Eidon-AI/eidon-tracker/whitepaper-styled.html

# EIDON TRACKER SYSTEM

## A High-Precision Wearable IMU Platform for Embodied AI Training Data Collection

Eidon Tracker - Technical illustration

Eidon Tracker - Technical illustration

Version 1.0 Date: November 2025

## Table of Contents

1. Executive Summary
2. System Overview
3. Hardware Platform
4. Firmware & Embedded Software
5. Data Collection & Processing Pipeline
6. Mathematical Framework
7. Integration Ecosystem
8. Applications & Use Cases
9. Technical Specifications
10. Conclusion

## 1. Executive Summary

### The Embodied AI Data Challenge

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

### The Eidon Solution

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

Key Value Propositions:

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

### The “LLM Moment” for Humanoid Robotics

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

## 2. System Overview

### Architecture

The Eidon ecosystem consists of three integrated subsystems:

System Architecture Diagram - Complete ecosystem from capture to training

System Architecture Diagram - Complete ecosystem from capture to training

#### 2.1 Eidon Tracker Hardware

Seven wearable IMU devices providing real-time orientation tracking:

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

#### 2.2 Mobile Application Hub

Smartphone app serving as central data aggregator:

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

#### 2.3 Data Processing Pipeline (eidon-sim)

Real-time and post-processing kinematics engine:

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

### Data Flow

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

┌─────────────────────────────────────────────────────────────────────┐
│  TRAINING PHASE (VLA Pipeline)                                      │
├─────────────────────────────────────────────────────────────────────┤
│  Processed Dataset ──► VLA Training ──► Humanoid Control Policy    │
└─────────────────────────────────────────────────────────────────────┘

### Wearing Configuration

Body Tracking Layout - Front and side view showing 7 tracker placement positions

Body Tracking Layout - Front and side view showing 7 tracker placement positions

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

Tracker Mounting Details - Close-up showing strap mounting and attachment mechanism

Tracker Mounting Details - Close-up showing strap mounting and attachment mechanism

### Key System Specifications (Summary)

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

## 3. Hardware Platform

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

### 3.1 Custom PCB Design

PCB Design - Custom circuit board layout and schematic

PCB Design - Custom circuit board layout and schematic

#### PCB Specifications

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

#### Key Components

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

#### Power Subsystem

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

#### Communication Interfaces

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

### 3.2 Mechanical Design

Exploded View Assembly - CAD rendering showing all components separated

Exploded View Assembly - CAD rendering showing all components separated

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

Exploded View Assembly - Side perspective showing internal layout

Exploded View Assembly - Side perspective showing internal layout

#### Enclosure Specifications

Current Design: Version 3b (eidon-tracker-v3b)

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

#### Mounting System

Arm Mount - Elastic strap mounting on forearm Chest Mount - Harness system for torso tracking

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

#### Manufacturing Considerations

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

### 3.3 Bill of Materials (Complete Device)

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

Complete 7-Device Kit (Ready to Use):

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

## 4. Firmware & Embedded Software

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

Firmware Architecture Diagram - Layered software architecture and data flow

### 4.1 Development Environment

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

### 4.2 Core Firmware Capabilities

#### A. IMU Sensor Integration

Sensor configuration (from firmware/lib/BNO085/BNO085.cpp):

// Initialize I2C communication at 400kHz
Wire.setPins(SDA_PIN, SCL_PIN);  // GPIO20, GPIO19
Wire.begin();
Wire.setClock(400000);

// Configure BNO085 for game rotation vector mode
bno08x.enableReport(SH2_GAME_ROTATION_VECTOR, 20833);  // 48Hz (20.83ms)

Data acquisition loop (48Hz):

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

#### B. Dual-Radio Wireless Architecture

The firmware implements a unique BLE + ESP-NOW dual-protocol system for efficient multi-device coordination.

BLE (Bluetooth Low Energy) - Primary Interface:

Custom GATT service: E1D00001-8B5A-3E5B-9E23-4F9B5C91BBDE

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

BLE notification rate: 24Hz (42ms intervals) to balance throughput and power

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

ESP-NOW - Child-to-Hub Communication:

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

Protocol details:

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

#### C. Device Role System

Seven role types (configured via BLE characteristic E1D00007):

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

#### D. Power Management

Battery monitoring (firmware/src/main.cpp):

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

Update interval: Every 5 seconds (balances accuracy and ADC power consumption)

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

#### E. LED Status Indicators

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

Auxiliary LED (GPIO1) - Secondary indicator: - Blinking: Advertising - Solid: Connected

### 4.3 Firmware Performance Metrics

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

### 4.4 Firmware File Structure

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

## 5. Data Collection & Processing Pipeline

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

### 5.1 Mobile Application Hub

Platform: iOS/Android (Flutter framework)

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

Mobile App Screenshot - Data collection interface with device status and recording controls

Mobile App Screenshot - Data collection interface with device status and recording controls

### 5.2 Quaternion Data Format

Raw quaternion packet (from BLE characteristic):

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

Device info packet (characteristic E1D00005):

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

### 5.3 eidon-sim Processing Engine

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

#### Core Processing Modules

A. Quaternion Decoder (src/core/reportParsers.ts)

Converts raw binary quaternion data to usable format:

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

Coordinate frame transformation (sensor → Three.js world):

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

B. Seven-Degree-of-Freedom Arm Solver (src/core/ArmSolver.ts)

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

Elbow joint (1-DOF): 4. Flex (flexion/extension angle)

Forearm (1-DOF): 5. Roll (pronation/supination)

Wrist joint (2-DOF): 6. Yaw (ulnar/radial deviation) 7. Pitch (flexion/extension)

Algorithmic approach (detailed in Section 6: Mathematical Framework)

C. 3D Skeletal Visualization (src/ui/scene/)

Two rendering modes:

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

D. Temporal Filtering

To reduce high-frequency noise from IMU drift and vibration:

Angle unwrapping (prevents discontinuities at ±180°):

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

Exponential moving average (EMA smoothing):

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

### 5.4 Output Data Products

The eidon-sim pipeline generates multiple output formats:

1. Joint Angle Time Series (CSV)

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

2. 3D Skeletal Positions (JSON)

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

3. Video with Overlay (MP4)

Synchronized video with: - On-screen joint angle readouts - Skeleton overlay (optional) - Timestamp and session metadata

4. VLA Training Format

Proposed structure (compatible with common VLA frameworks):

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

Action labeling: - Manual annotation via UI timeline - Future: GPT-4V automatic segmentation from video

## 6. Mathematical Framework

This section details the mathematical transformations that convert raw IMU quaternions into anatomically meaningful joint angles.

Quaternion to Angles Overview - Mathematical transformation pipeline

### 6.1 Quaternion Fundamentals

Definition:

A quaternion q is a 4-dimensional number representing 3D rotation:

q = w + xi + yj + zk

where i² = j² = k² = ijk = -1

Vector form: q = [x, y, z, w] (or [qx, qy, qz, qw])

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

Quaternion multiplication (Hamilton product):

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

Rotating a vector v by quaternion q:

v' = q ⊗ [0, v] ⊗ q⁻¹

Implemented efficiently as:

vec3.transformQuat(out, v, q)

### 6.2 Quaternion to Rotation Matrix

The quaternion q = [x, y, z, w] converts to a 3×3 rotation matrix:

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

Code implementation (src/core/mathUtils.ts):

export function quatToMat3(q: quat): mat3 {
  const m = mat3.create();
  mat3.fromQuat(m, q);
  return m;
}

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

### 6.3 Euler Angle Extraction

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

#### A. Z-Y-X Euler Angles (Shoulder)

Used for shoulder joint angles (ISB biomechanics convention).

Mathematical derivation:

Given rotation matrix R from quaternion, extract angles:

R = Rz(α) · Ry(β) · Rx(γ)

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

Solving for Euler angles:

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

Code implementation (src/core/mathUtils.ts:9-23):

export function eulerZYX(q: quat): [number, number, number] {
  const m = mat3.fromQuat(mat3.create(), q);

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

  return [yaw, pitch, roll];  // Radians
}

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

#### B. X-Y-Z Euler Angles (Wrist)

Alternative convention for wrist joint (avoids gimbal lock in different configuration).

Direct quaternion formula (avoids matrix conversion):

export function eulerXYZ(q: quat): [number, number, number] {
  const [x, y, z, w] = q;

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

  const pitch = Math.asin(Math.max(-1, Math.min(1, 2.0 * (w * y - z * x))));

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

  return [yaw, roll, pitch];  // Note: pitch/roll swapped to match convention
}

### 6.4 Vector-Based Angle Calculations

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

#### Elbow Flexion Angle

Mathematical formula:

Given unit vectors u (upper arm forward) and l (forearm forward):

θ = arccos(u · l)

where u · l = ux·lx + uy·ly + uz·lz (dot product)

Code implementation (src/core/mathUtils.ts:74-79):

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

  return Math.acos(clampedCos) * 180 / Math.PI;
}

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

Anatomical interpretation: - 0° = Full extension (arm straight) - 90° = Right angle - 145° = Typical maximum flexion

### 6.5 Forearm Roll (Pronation/Supination)

Challenge: Measuring twist of forearm about its long axis while elbow bends.

Naive approach fails: Simply comparing quaternions gives coupled elbow+roll motion.

Robust solution: Project “up” vectors onto plane perpendicular to forearm forward direction.

Mathematical steps:

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

up_upper_proj = up_upper − (up_upper · fwd_forearm) · fwd_forearm
3. Project forearm up vector onto same plane:

up_forearm_proj = up_forearm − (up_forearm · fwd_forearm) · fwd_forearm
4. Calculate angle between projections:

θ = arccos(up_upper_proj · up_forearm_proj / (‖up_upper_proj‖ · ‖up_forearm_proj‖))
5. Determine sign using cross product:

sign = (up_upper_proj × up_forearm_proj) · fwd_forearm ≥ 0 ? −1 : 1

Code implementation (src/core/ArmSolver.ts:114-158):

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

vec3.normalize(upperUpProj, upperUpProj);
vec3.normalize(lowerUpProj, lowerUpProj);

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

const forearmRollDeg = sign * angle * 180 / Math.PI;

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

### 6.6 Relative Quaternion Method (Wrist Angles)

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

Mathematical approach:

Given forearm quaternion q_forearm and hand quaternion q_hand:

1. Calculate relative rotation:

q_wrist = q_forearm⁻¹ ⊗ q_hand
2. Extract Euler angles from q_wrist using Z-Y-X convention

Code implementation (src/core/ArmSolver.ts:162-184):

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

// Extract wrist Euler angles
const [wristYaw, wristRoll, wristPitch] = eulerZYX(Q_Wrist);

// Convert radians to degrees
const wristYawDeg = wristYaw * 180 / Math.PI;
const wristPitchDeg = wristPitch * 180 / Math.PI;

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

### 6.7 Complete Seven-Angle Solver

Summary of derivation pipeline for one arm:

Inputs: Q_UpperArm, Q_Forearm, Q_Hand (3 quaternions)

1. Shoulder angles (3-DOF):
   [yaw, pitch, roll] = eulerZYX(Q_UpperArm) * 180/π

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

Outputs: [sh_yaw, sh_pitch, sh_roll, el_flex, fr_roll, wr_yaw, wr_pitch]

### 6.8 Forward Kinematics (Vector Chaining)

Once joint angles are known, we can reconstruct 3D joint positions using forward kinematics.

Chain structure:

Shoulder (fixed) → [Upper Arm] → Elbow → [Forearm] → Wrist → [Hand] → Fingertips

Position calculation:

P_shoulder = [±0.3, 1.4, 0.0]  (left/right offset from chest)

P_elbow = P_shoulder + L_humerus · fwd_upper

P_wrist = P_elbow + L_radius · fwd_forearm

P_fingertips = P_wrist + L_hand · fwd_hand

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

Code implementation (src/ui/scene/vectorArm.ts:144-154):

const shoulder: vec3 = this.side === 'left' ? [-0.3, 1.4, 0] : [0.3, 1.4, 0];

const elbowPos = vec3.scaleAndAdd(
  vec3.create(),
  shoulder,
  upperArmForward,
  HUM_LEN()
);

const wristPos = vec3.scaleAndAdd(
  vec3.create(),
  elbowPos,
  forearmForward,
  RAD_LEN()
);

const fingertipPos = vec3.scaleAndAdd(
  vec3.create(),
  wristPos,
  handForward,
  HAND_LEN()
);

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

## 7. Integration Ecosystem

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

### 7.1 VLA Training Pipeline Integration

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

Integration approach:

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

Example: OpenVLA integration pseudocode

from eidon import EidonDataset
from openvla import VLATrainer

# Load Eidon dataset
dataset = EidonDataset("path/to/collected_data/")

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

# Train VLA model
trainer = VLATrainer(config)
trainer.train(vla_episodes)

### 7.2 Robotic Platform Retargeting

Challenge: Human arm kinematics ≠ robot arm kinematics

Solutions:

A. Direct Joint Mapping (for humanoid robots)

If robot has similar kinematic structure (7-DOF arms):

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

B. Cartesian Task Space Mapping

For robots with different DOF (e.g., 6-DOF industrial arms):

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

# Solve inverse kinematics for robot
robot_joint_angles = robot.ik_solver(
    target_pos=wrist_position_3d,
    target_ori=wrist_orientation_quat,
)
robot.set_joint_targets(robot_joint_angles)

C. Reinforcement Learning Refinement

Use human demonstrations as initialization for RL policy:

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

### 7.3 Simulation Environment Integration

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

Example: Isaac Sim replay

from omni.isaac.kit import SimulationApp
from eidon import EidonDataset

# Load dataset
dataset = EidonDataset("data/task_demonstrations/")

# Spawn humanoid asset in Isaac Sim
humanoid = spawn_humanoid("eidon_humanoid.usd")

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

### 7.4 Real-Time Teleoperation

Architecture:

Human + Eidon Trackers → Mobile App → WebSocket Server → Robot Controller → Actuators
                         (BLE)        (WiFi/LTE)          (ROS2/MQTT)

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

### 7.5 Data Annotation & Labeling

Collected datasets require task-level annotations for VLA training.

Annotation workflow:

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

### 7.6 API Specification

For developers integrating Eidon data:

Dataset loader (Python)

from eidon import EidonDataset

# Load dataset from directory
dataset = EidonDataset("path/to/dataset/")

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

BLE connection (TypeScript/JavaScript)

import { EidonBLEDevice } from '@eidon/ble-sdk';

// Scan for devices
const devices = await EidonBLEDevice.scan();

// Connect to specific device
const tracker = await EidonBLEDevice.connect(devices[0]);

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

// Trigger calibration
await tracker.calibrate();

// Read battery level
const battery = await tracker.getBatteryPercent();
console.log(`Battery: ${battery}%`);

## 8. Applications & Use Cases

The Eidon Tracker platform enables a wide range of applications beyond VLA training.

### 8.1 Embodied AI Training Data Collection

Primary use case: Create large-scale datasets of human task demonstrations for robot learning.

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

### 8.2 Teleoperation for Remote Robotics

Scenario: Control humanoid robot from remote location

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

### 8.3 Biomechanics Research

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

### 8.4 Animation & Virtual Production

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

### 8.5 Physical Therapy & Rehabilitation

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

## 9. Technical Specifications

### 9.1 Hardware Specifications

#### Eidon Tracker Device

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

#### Microcontroller (ESP32-C6)

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

#### IMU (BNO085)

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

#### Power System

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

#### Communication

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

### 9.2 Firmware Specifications

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

### 9.3 Data Format Specifications

#### Quaternion Data

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

#### Joint Angles (per arm)

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

### 9.4 System Requirements

#### Mobile Application

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

#### eidon-sim Processing

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

### 9.5 Manufacturing Specifications

#### PCB

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

#### 3D Printed Enclosure

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

## 10. Conclusion

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

### Key Innovations

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

### The Path Forward

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

### Closing Statement

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

## Appendix A: Bill of Materials (Detailed)

### Per-Device BOM (Current Production Costs)

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

### Complete 7-Device System BOM

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

### Volume Pricing Estimates

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

## Appendix B: File Locations Reference

### eidon-tracker Repository

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

### eidon-sim Repository

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

## Appendix C: UUID Reference

### BLE Service UUIDs

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

Legend: - R = Read - W = Write - N = Notify - RN = Read + Notify - RW = Read + Write

## Appendix D: Glossary

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

BNO085: Bosch 9-DOF IMU with hardware sensor fusion. Outputs quaternions at 48Hz.

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

Embodied AI: AI systems that interact with the physical world through robotic bodies.

ESP-NOW: Espressif’s proprietary low-latency wireless protocol. Used for child device → hub communication.

Euler Angles: Representation of 3D rotation as three sequential axis rotations (e.g., yaw-pitch-roll).

GATT (Generic Attribute Profile): BLE protocol layer defining service/characteristic structure.

Gimbal Lock: Singularity in Euler angle representation where two axes align, losing a degree of freedom.

IMU (Inertial Measurement Unit): Sensor combining gyroscope, accelerometer, and magnetometer. Measures orientation and acceleration.

NimBLE: Lightweight Bluetooth stack for ESP32 (alternative to Bluedroid).

Pronation/Supination: Forearm rotation (pronation = palm down, supination = palm up).

Quaternion: 4D number (w, x, y, z) representing 3D rotation. Avoids gimbal lock, efficient for interpolation.

RISC-V: Open-source instruction set architecture. Used in ESP32-C6 microcontroller.

ROM (Range of Motion): Maximum angular extent a joint can move.

Sensor Fusion: Combining data from multiple sensors (gyro, accel, mag) to compute accurate orientation.

VLA (Vision-Language-Action): Multimodal AI model mapping visual observations + language instructions → robot actions.

## Appendix E: Contact & Licensing

Company: Eidon Website: www.eidon.ai Technical Support: robert@eidon.ai GitHub: github.com/eidon/eidon-tracker

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

Commercial licensing available for: - White-label OEM integration - Custom firmware development - Enterprise support contracts

## Appendix F: Hardware Schematics

### KiCad Schematic Diagram

Complete electrical schematic showing circuit design, component interconnections, and signal routing.

KiCad Schematic - Complete electrical circuit design

KiCad Schematic - Complete electrical circuit design

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

For full resolution schematic and PCB layout files, see: pcb/eidon-tracker/eidon-tracker.kicad_sch

Document prepared by: Eidon Engineering Team Last updated: November 2025 Document version: 1.0
