Eidon-AI/eidon-tracker/docs/README.md

# Eidon Tracker Documentation

This directory contains technical documentation for the Eidon Tracker project, including firmware specifications, hardware details, and integration guides.

## Documentation Index

### 1. [GATT Service Reference](./GATT_SERVICE_REFERENCE.md)
Complete reference for the custom BLE GATT service implementation, including:
- Service and Characteristic UUIDs
- Data formats and structures
- Flutter/Dart code examples
- Connection parameters and best practices

### 2. [Hardware Overview](./HARDWARE_OVERVIEW.md)
Technical specifications and pinout information for the Eidon Tracker hardware.

### 3. [Firmware Architecture](./FIRMWARE_ARCHITECTURE.md)
Overview of the firmware structure, build process, and key components.

### 4. [Mobile App Integration Guide](./MOBILE_APP_INTEGRATION.md)
Step-by-step guide for integrating Eidon Tracker devices with mobile applications.

### 5. [Troubleshooting Guide](./TROUBLESHOOTING.md)
Common issues and solutions for firmware, hardware, and connectivity problems.

## Quick Links

- **Firmware Source**: `/firmware/src/main.cpp`
- **Platform Configuration**: `/firmware/platformio.ini`
- **Mobile App**: Flutter application for iOS/Android
- **Hardware**: Based on XIAO nRF52840 Sense with BNO085 IMU

## Version Information

- Current Firmware Version: 1.2
- Hardware Revision: 1.2
- Documentation Last Updated: 2024
