Eidon-AI/eidon-tracker/images/whitepaper/MOBILE_APP_SCREENSHOT.jpg

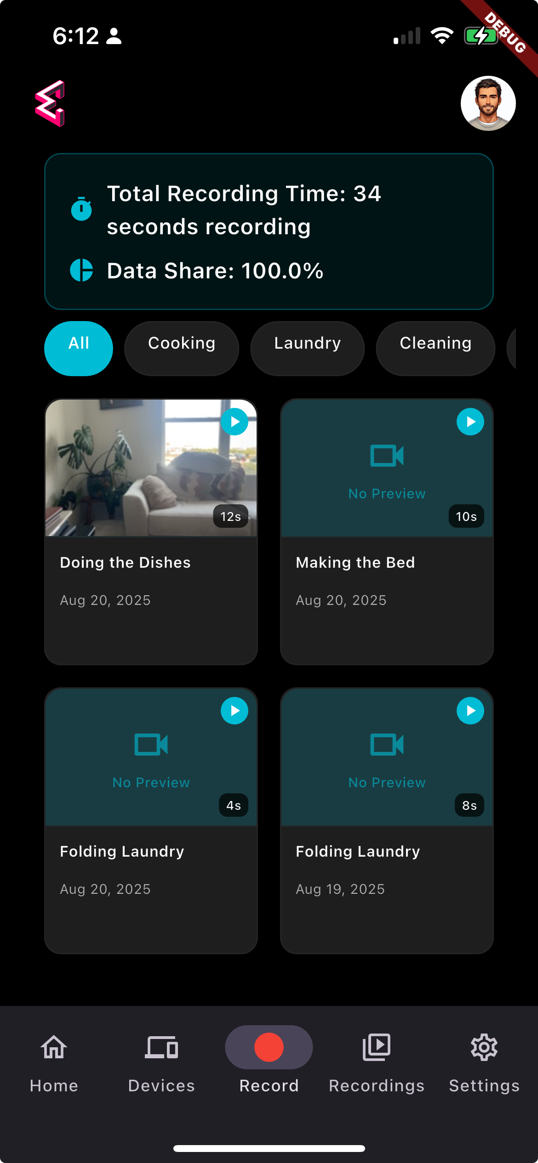
images/whitepaper/MOBILE_APP_SCREENSHOT.jpg
