Eidon-AI/eidon-tracker/cad/eidon-tracker-mount-arm.3mf

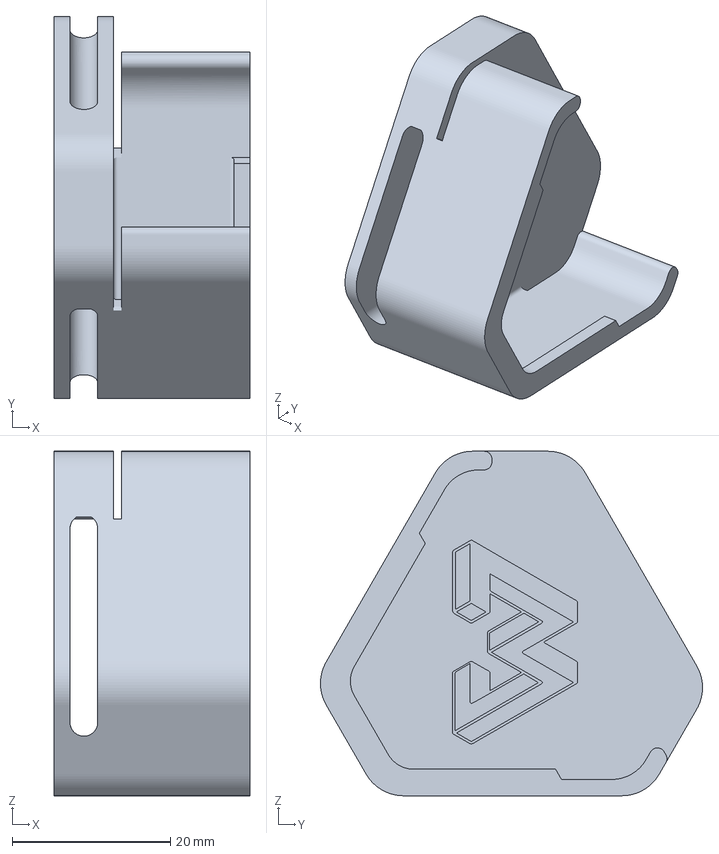
[picture p29: CAD file, 2025-08-28]
cad/eidon-tracker-mount-arm.3mf
24.7 x 48.3 x 43.6 mm
