Eidon-AI/eidon-tracker/cad/eidon-tracker-mount-chest.3mf

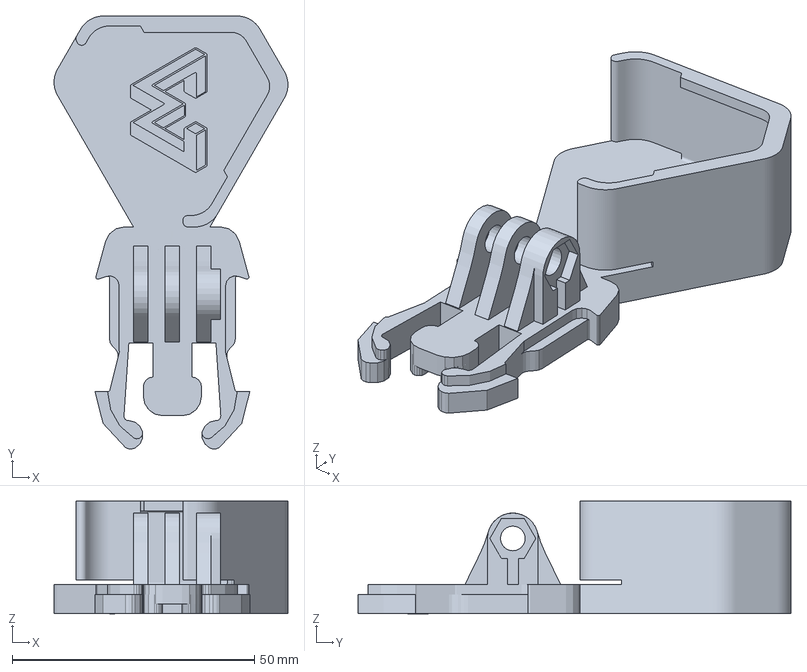
[picture p30: CAD file, 2025-08-28]
cad/eidon-tracker-mount-chest.3mf
48.3 x 89.5 x 23.2 mm
