Eidon-AI/eidon-tracker/cad/eidon-tracker-base.stl

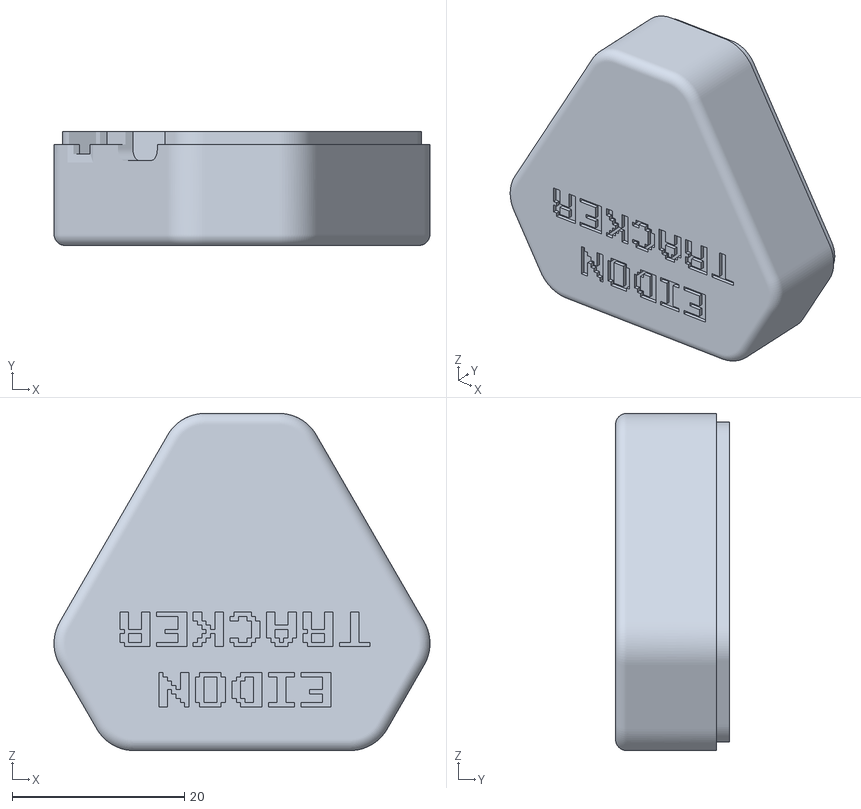
[picture p31: CAD file, 2025-07-09]
cad/eidon-tracker-base.stl
43.7 x 13.2 x 39.2
