Eidon-AI/eidon-tracker/cad/eidon-tracker-top.stl

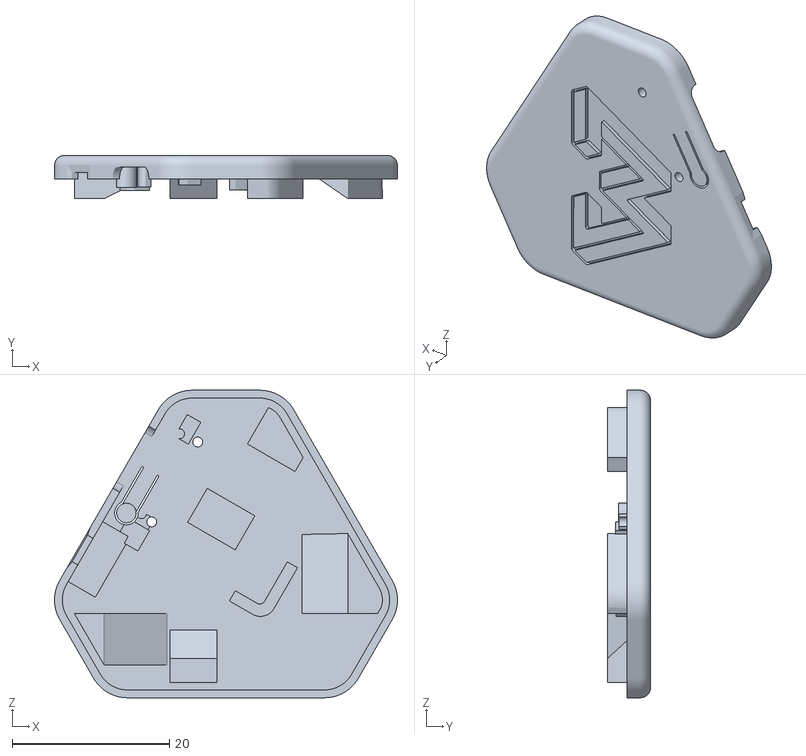
[picture p32: CAD file, 2025-07-09]
cad/eidon-tracker-top.stl
43.7 x 5.50 x 39.2
