Eidon-AI/eidon-tracker/cad/eidon-tracker-batch-chest.3mf

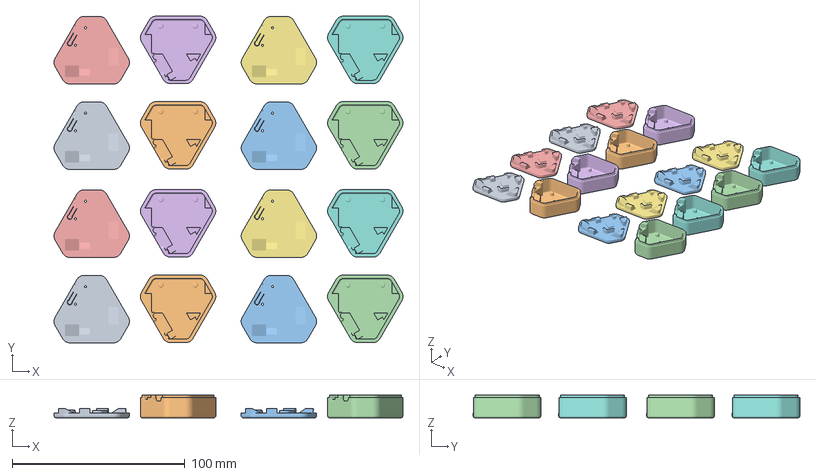
[picture p33: CAD file, 2025-07-09]
cad/eidon-tracker-batch-chest.3mf
202.0 x 189.2 x 13.2 mm
eidon-tracker-top.stl x 8
eidon-tracker-base.stl x 8
