Eidon-AI/eidon-tracker/cad/eidon-tracker-batch-arms.3mf

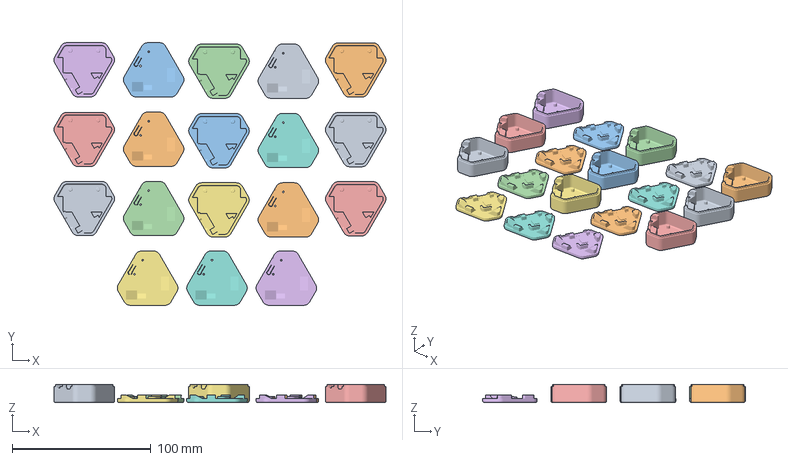
[picture p34: CAD file, 2025-07-09]
cad/eidon-tracker-batch-arms.3mf
239.3 x 189.3 x 13.2 mm
eidon-tracker-base.stl x 9
eidon-tracker-top-1.stl x 3
eidon-tracker-top-2.stl x 3
eidon-tracker-top.stl x 3
