Eidon-AI/eidon-tracker/cad/eidon-tracker-batch-mount.3mf

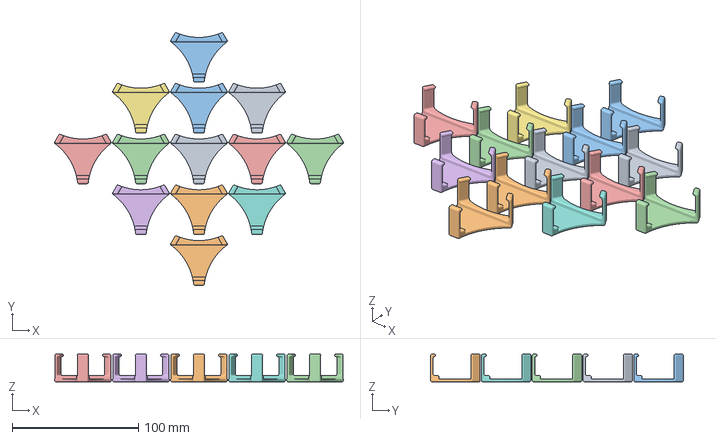
[picture p35: CAD file, 2025-07-09]
cad/eidon-tracker-batch-mount.3mf
229.1 x 200.3 x 22.1 mm
eidon-tracker-mount.stl x 13
