Eidon-AI/eidon-tracker/firmware/src/BLE_Services/BLE_Polling_Service.cpp

#include "BLE_Polling_Service.h"
#include <Arduino.h>
#include <NimBLEDevice.h>
#include "DeviceConfig.h"
#include "BNO085.h"
#include "Role_Services/RoleConfig_Service.h"
#include "Role_Services/HubClient_Service.h"

// Forward declarations
class BNO085;
class DeviceConfig;
class ColorManager;

// ESP-NOW function declarations (for child devices)
extern bool initializeESPNowSender();
extern void updateESPNowHubMacAddress();
extern void sendCalibrationCommand();

// Hub client service function declarations
extern void setupHubClientService();

// External variables that handlers need access to
extern BNO085 imu;
extern DeviceConfig deviceConfig;
extern NimBLECharacteristic* roleConfigChar;
extern NimBLECharacteristic* calibrationChar;
extern bool deviceConnected;
extern HubClientService hubClientService;

// Global instance
BLEPollingManager pollingManager;

// Default polling intervals
const unsigned long DEFAULT_ROLE_INTERVAL = 200;      // 5Hz
const unsigned long DEFAULT_CALIBRATION_INTERVAL = 100; // 10Hz
const unsigned long DEFAULT_COLOR_INTERVAL = 150;     // ~7Hz

// Battery mode intervals (slower to save power)
const unsigned long BATTERY_ROLE_INTERVAL = 500;      // 2Hz
const unsigned long BATTERY_CALIBRATION_INTERVAL = 250; // 4Hz
const unsigned long BATTERY_COLOR_INTERVAL = 300;     // ~3Hz

// Performance mode intervals (faster for responsiveness)
const unsigned long PERFORMANCE_ROLE_INTERVAL = 100;  // 10Hz
const unsigned long PERFORMANCE_CALIBRATION_INTERVAL = 50; // 20Hz
const unsigned long PERFORMANCE_COLOR_INTERVAL = 75;  // ~13Hz

bool BLEPollingManager::begin() {
    if (initialized) return true;
    
    // Initialize all targets
    for (int i = 0; i < MAX_TARGETS; i++) {
        targets[i].characteristic = nullptr;
        targets[i].lastValue = "";
        targets[i].lastCheck = 0;
        targets[i].interval = 0;
        targets[i].handler = nullptr;
        targets[i].name = nullptr;
        targets[i].enabled = false;
        targets[i].consecutiveFailures = 0;
        targets[i].maxFailures = 5; // Default max failures
        targets[i].stats = PollingStats();
    }
    
    targetCount = 0;
    initialized = true;
    

    return true;
}

void BLEPollingManager::update() {
    if (!initialized) return;
    
    unsigned long currentTime = millis();
    
    for (int i = 0; i < targetCount; i++) {
        PollingTarget& target = targets[i];
        
        // Skip disabled targets
        if (!target.enabled) continue;
        
        // Check if it's time to poll this target
        if (currentTime - target.lastCheck >= target.interval) {
            unsigned long pollStartTime = currentTime;
                       
            // Attempt to read characteristic value
            std::string currentValue;
            bool success = false;
            
            if (target.characteristic != nullptr) {
                currentValue = target.characteristic->getValue();
                success = true; // Assume success if we got a value
            } else {
                success = false;
                target.consecutiveFailures++;
            }
            
            // Calculate response time
            unsigned long responseTime = millis() - pollStartTime;
            
            // Update statistics
            updateStats(target, success, responseTime);
            
            // Check if value changed
            if (success && currentValue != target.lastValue) {
                if (debugMode) {
                    Serial.printf("Polling %s: value changed, length=%d\n", 
                                 target.name, currentValue.length());
                }
                
                // Update statistics for successful change
                target.stats.successfulChanges++;
                target.stats.lastChangeTime = millis();
                
                // Call handler with new value
                if (target.handler) {
                    target.handler(currentValue, true);
                }
                
                target.lastValue = currentValue;
                target.consecutiveFailures = 0; // Reset failure counter on success
            } else if (!success) {
                // Handle failure
                if (target.consecutiveFailures >= target.maxFailures) {
                    Serial.printf("Polling failed for %s after %lu attempts\n", 
                                target.name, target.maxFailures);
                    
                    // Call handler with failure
                    if (target.handler) {
                        target.handler("", false);
                    }
                }
            }
            
            // Update last check time
            target.lastCheck = currentTime;
        }
    }
}

bool BLEPollingManager::addTarget(NimBLECharacteristic* characteristic, unsigned long interval, 
                                  std::function<void(const std::string&, bool)> handler, const char* name) {
    if (!initialized) {
        Serial.println("Polling Manager not initialized!");
        return false;
    }
    
    if (targetCount >= MAX_TARGETS) {
        Serial.printf("Cannot add target %s: maximum targets reached (%d)\n", name, MAX_TARGETS);
        return false;
    }
    
    // Check if target with this name already exists
    if (findTarget(name) != nullptr) {
        Serial.printf("Target %s already exists!\n", name);
        return false;
    }
    
    // Add new target
    PollingTarget& target = targets[targetCount];
    target.characteristic = characteristic;
    target.lastValue = "";
    target.lastCheck = 0;
    target.interval = interval;
    target.handler = handler;
    target.name = name;
    target.enabled = true;
    target.consecutiveFailures = 0;
    target.maxFailures = 5;
    target.stats = PollingStats();
    
    targetCount++;
    

    return true;
}

bool BLEPollingManager::removeTarget(const char* name) {
    PollingTarget* target = findTarget(name);
    if (!target) {
        Serial.printf("Target %s not found for removal\n", name);
        return false;
    }
    
    // Shift remaining targets down
    int targetIndex = target - targets;
    for (int i = targetIndex; i < targetCount - 1; i++) {
        targets[i] = targets[i + 1];
    }
    
    // Clear the last target
    targets[targetCount - 1] = PollingTarget();
    targetCount--;
    
    Serial.printf("Removed polling target: %s\n", name);
    return true;
}

void BLEPollingManager::enableTarget(const char* name) {
    PollingTarget* target = findTarget(name);
    if (target) {
        target->enabled = true;
        Serial.printf("Enabled polling target: %s\n", name);
    } else {
        Serial.printf("Target %s not found for enable\n", name);
    }
}

void BLEPollingManager::disableTarget(const char* name) {
    PollingTarget* target = findTarget(name);
    if (target) {
        target->enabled = false;
        Serial.printf("Disabled polling target: %s\n", name);
    } else {
        Serial.printf("Target %s not found for disable\n", name);
    }
}

void BLEPollingManager::setInterval(const char* name, unsigned long interval) {
    PollingTarget* target = findTarget(name);
    if (target) {
        target->interval = interval;
        Serial.printf("Set polling interval for %s: %lu ms\n", name, interval);
    } else {
        Serial.printf("Target %s not found for interval change\n", name);
    }
}

void BLEPollingManager::setBatteryMode(bool lowBattery) {
    batteryMode = lowBattery;
    if (lowBattery) {
        Serial.println("Switching to battery mode (slower polling)");
        adjustIntervalsForBatteryMode();
    } else {
        Serial.println("Switching to normal mode");
        adjustIntervalsForPerformanceMode();
    }
}

void BLEPollingManager::setPerformanceMode(bool highPerformance) {
    performanceMode = highPerformance;
    if (highPerformance) {
        Serial.println("Switching to performance mode (faster polling)");
        adjustIntervalsForPerformanceMode();
    } else {
        Serial.println("Switching to normal mode");
        adjustIntervalsForPerformanceMode();
    }
}

void BLEPollingManager::printStats() {
    Serial.println("=== BLE Polling Statistics ===");
    for (int i = 0; i < targetCount; i++) {
        const PollingTarget& target = targets[i];
        const PollingStats& stats = target.stats;
        
        Serial.printf("%s: %lu polls, %lu changes, %lu fails, enabled=%d\n",
                     target.name, stats.totalPolls, stats.successfulChanges, 
                     stats.failedReads, target.enabled);
    }
}

void BLEPollingManager::printDetailedStats() {
    Serial.println("=== Detailed BLE Polling Statistics ===");
    for (int i = 0; i < targetCount; i++) {
        const PollingTarget& target = targets[i];
        const PollingStats& stats = target.stats;
        
        Serial.printf("%s:\n", target.name);
        Serial.printf("  Total polls: %lu\n", stats.totalPolls);
        Serial.printf("  Successful changes: %lu\n", stats.successfulChanges);
        Serial.printf("  Failed reads: %lu\n", stats.failedReads);
        Serial.printf("  Last change: %lu ms ago\n", millis() - stats.lastChangeTime);
        Serial.printf("  Average response time: %lu ms\n", stats.averageResponseTime);
        Serial.printf("  Current interval: %lu ms\n", target.interval);
        Serial.printf("  Consecutive failures: %lu\n", target.consecutiveFailures);
        Serial.printf("  Enabled: %s\n", target.enabled ? "YES" : "NO");
        Serial.println();
    }
}

void BLEPollingManager::resetStats(const char* name) {
    PollingTarget* target = findTarget(name);
    if (target) {
        target->stats = PollingStats();
        Serial.printf("Reset statistics for %s\n", name);
    } else {
        Serial.printf("Target %s not found for stats reset\n", name);
    }
}

void BLEPollingManager::resetAllStats() {
    for (int i = 0; i < targetCount; i++) {
        targets[i].stats = PollingStats();
    }
    Serial.println("Reset all polling statistics");
}

bool BLEPollingManager::isTargetEnabled(const char* name) const {
    const PollingTarget* target = findTarget(name);
    return target ? target->enabled : false;
}

unsigned long BLEPollingManager::getTargetInterval(const char* name) const {
    const PollingTarget* target = findTarget(name);
    return target ? target->interval : 0;
}

// Private helper methods
BLEPollingManager::PollingTarget* BLEPollingManager::findTarget(const char* name) {
    for (int i = 0; i < targetCount; i++) {
        if (targets[i].name && strcmp(targets[i].name, name) == 0) {
            return &targets[i];
        }
    }
    return nullptr;
}

const BLEPollingManager::PollingTarget* BLEPollingManager::findTarget(const char* name) const {
    for (int i = 0; i < targetCount; i++) {
        if (targets[i].name && strcmp(targets[i].name, name) == 0) {
            return &targets[i];
        }
    }
    return nullptr;
}

void BLEPollingManager::adjustIntervalsForBatteryMode() {
    for (int i = 0; i < targetCount; i++) {
        PollingTarget& target = targets[i];
        
        if (strcmp(target.name, "Role") == 0) {
            target.interval = BATTERY_ROLE_INTERVAL;
        } else if (strcmp(target.name, "Calibration") == 0) {
            target.interval = BATTERY_CALIBRATION_INTERVAL;
        } else if (strcmp(target.name, "Color") == 0) {
            target.interval = BATTERY_COLOR_INTERVAL;
        }
    }
}

void BLEPollingManager::adjustIntervalsForPerformanceMode() {
    for (int i = 0; i < targetCount; i++) {
        PollingTarget& target = targets[i];
        
        if (strcmp(target.name, "Role") == 0) {
            target.interval = PERFORMANCE_ROLE_INTERVAL;
        } else if (strcmp(target.name, "Calibration") == 0) {
            target.interval = PERFORMANCE_CALIBRATION_INTERVAL;
        } else if (strcmp(target.name, "Color") == 0) {
            target.interval = PERFORMANCE_COLOR_INTERVAL;
        }
    }
}

void BLEPollingManager::updateStats(PollingTarget& target, bool success, unsigned long responseTime) {
    PollingStats& stats = target.stats;
    stats.totalPolls++;
    
    if (success) {
        // Note: We don't track changes here since that's handled in the main polling loop
        // where we have proper type conversion
    } else {
        stats.failedReads++;
    }
    
    // Update average response time
    stats.totalResponseTime += responseTime;
    stats.averageResponseTime = stats.totalResponseTime / stats.totalPolls;
}

// ============================================================================
// Handler Function Implementations
// ============================================================================

// State validation function to ensure characteristic matches device state
void validateRoleConfigState() {
    if (roleConfigChar == nullptr) return;
    
    std::string currentValue = roleConfigChar->getValue();
    DeviceRole actualRole = deviceConfig.getRole();
    
    // Check if characteristic matches device state
    bool needsUpdate = false;
    
    if (currentValue.length() == sizeof(RoleConfigData)) {
        // Full struct - check if it matches current state
        RoleConfigData* data = (RoleConfigData*)currentValue.data();
        if (data->role != (uint8_t)actualRole) {
            needsUpdate = true;
        }
        
        // Check if hub MAC address matches
        if (deviceConfig.isHubMacAssigned()) {
            uint8_t storedMac[6];
            deviceConfig.getHubMacAddress(storedMac);
            if (memcmp(data->hubMacAddress, storedMac, 6) != 0) {
                needsUpdate = true;
            }
        } else if (!deviceConfig.isAllZerosMacAddress(data->hubMacAddress)) {
            needsUpdate = true;
        }
    } else if (currentValue.length() != 1) {
        // Unexpected format - reset to current state
        needsUpdate = true;
    }
    
    if (needsUpdate) {
        Serial.println("Role Config: State mismatch detected, updating characteristic");
        updateRoleConfigCharacteristic();
    }
}

void handleRoleChange(const std::string& value, bool success) {
    if (!success) {
        Serial.println("Role Change: Failed to read characteristic value");
        return;
    }
    
    // Handle enhanced role assignment (client writes full RoleConfigData structure)
    if (value.length() == sizeof(RoleConfigData)) {
        RoleConfigData* data = (RoleConfigData*)value.data();
        uint8_t newRole = data->role;
        
        // Validate role value (0-6 are valid roles: LEFT_HAND, RIGHT_HAND, LEFT_FOREARM, RIGHT_FOREARM, LEFT_SHOULDER, RIGHT_SHOULDER, CHEST; 255 is ROLE_UNKNOWN)
        if (newRole <= 6 || newRole == 255) {
            Serial.printf("ROLE CHANGE: %s\n", deviceConfig.getRoleName((DeviceRole)newRole));
            
            // Validate and set hub MAC address if provided
            // Only clear if explicitly all zeros AND this is a child device that needs a hub
            bool needsHubMac = (newRole == ROLE_LEFT_HAND || newRole == ROLE_LEFT_FOREARM || newRole == ROLE_LEFT_SHOULDER);
            
            if (!deviceConfig.isAllZerosMacAddress(data->hubMacAddress)) {
                if (deviceConfig.isValidMacAddress(data->hubMacAddress)) {
                    deviceConfig.setHubMacAddress(data->hubMacAddress);
                    Serial.printf("ROLE CHANGE: Hub MAC address set: %02X:%02X:%02X:%02X:%02X:%02X\n",
                                 data->hubMacAddress[0], data->hubMacAddress[1], data->hubMacAddress[2],
                                 data->hubMacAddress[3], data->hubMacAddress[4], data->hubMacAddress[5]);
                } else {
                    Serial.println("ROLE CHANGE: Invalid hub MAC address provided, keeping existing");
                }
            } else if (needsHubMac) {
                // Only clear if this is a child device that needs a hub MAC
                // Don't clear if it's a hub device (hubs don't need hub MACs)
                deviceConfig.clearHubMacAddress();
                Serial.println("ROLE CHANGE: Hub MAC address cleared (all zeros provided for child device)");
            }
            
            // Apply the role change
            if (deviceConfig.setRole((DeviceRole)newRole)) {
                
                // 1. Update characteristic with full struct (state management)
                updateRoleConfigCharacteristic();
                
                // 2. Update advertising data with new role
                updateAdvertisingData();
                
                // 3. Handle child behavior - disconnect from phone when LEFT CHILD role assigned
                // Left children (hand, forearm, shoulder) send data to their corresponding right hub
                if (deviceConfig.isNodeMode() && (newRole == ROLE_LEFT_HAND || newRole == ROLE_LEFT_FOREARM || 
                                                 newRole == ROLE_LEFT_SHOULDER)) {
                    // Initialize ESP-NOW communication with assigned right hub
                    if (initializeESPNowSender()) {
                        updateESPNowHubMacAddress();
                    }
                    
                    // Disconnect from current phone connection if connected
                    if (deviceConnected) {
                        // Force disconnect by stopping advertising and restarting with updated data
                        NimBLEDevice::getAdvertising()->stop();
                        delay(100); // Brief delay to ensure disconnect
                        updateAdvertisingData(); // Restart advertising with updated role information
                    }
                }
                
                // 4. Handle hub behavior - initialize hub client service when HUB role assigned
                // Right hubs (hand, forearm, shoulder) receive data from left children
                // Chest has no children, so skip hub client service initialization
                if (deviceConfig.isHubMode() && (newRole == ROLE_RIGHT_HAND || newRole == ROLE_RIGHT_FOREARM || 
                                                 newRole == ROLE_RIGHT_SHOULDER)) {
                    // Initialize hub client service to receive ESP-NOW data from left children
                    setupHubClientService();
                }
                
                // 5. Provide LED feedback
                // TODO: Check LED feedback is working
                startRoleChangeLEDPattern();
                
            } else {
                Serial.println("ROLE CHANGE: Failed to apply");
            }
        } else {
            Serial.printf("ROLE CHANGE: Invalid role value: %d\n", newRole);
        }
    }
    // Handle single-byte role assignment (backward compatibility)
    else if (value.length() == 1) {
        uint8_t newRole = (uint8_t)value[0];
        
        // Validate role value (0-6 are valid roles: LEFT_HAND, RIGHT_HAND, LEFT_FOREARM, RIGHT_FOREARM, LEFT_SHOULDER, RIGHT_SHOULDER, CHEST; 255 is ROLE_UNKNOWN)
        if (newRole <= 6 || newRole == 255) {
            
            // Clear hub MAC address for legacy role assignment
            deviceConfig.clearHubMacAddress();
            
            // Apply the role change
            if (deviceConfig.setRole((DeviceRole)newRole)) {
                
                // 1. Update characteristic with full struct (state management)
                updateRoleConfigCharacteristic();
                
                // 2. Update advertising data with new role
                updateAdvertisingData();
                
                // 3. Handle child behavior - disconnect from phone when LEFT CHILD role assigned
                // Left children (hand, forearm, shoulder) send data to their corresponding right hub
                if (deviceConfig.isNodeMode() && (newRole == ROLE_LEFT_HAND || newRole == ROLE_LEFT_FOREARM || 
                                                 newRole == ROLE_LEFT_SHOULDER)) {
                    Serial.println("=== CHILD BEHAVIOR: Left child role assigned ===");
                    Serial.println("Left child device will send data to corresponding right hub via ESP-NOW");
                    
                    // Disconnect from current phone connection if connected
                    if (deviceConnected) {
                        Serial.println("Child: Disconnecting from phone...");
                        // Force disconnect by stopping advertising and restarting with updated data
                        NimBLEDevice::getAdvertising()->stop();
                        delay(100); // Brief delay to ensure disconnect
                        updateAdvertisingData(); // Restart advertising with updated role information
                        Serial.println("Child: Disconnected from phone, now advertising for hub connection");
                    }
                    
                    // Child devices should continue advertising normally
                    // They will accept connections from both phones and hubs
                    // The hub will be the one doing the seeking and connecting
                }
                
                // 4. Handle hub behavior - initialize hub client service when HUB role assigned
                // Right hubs (hand, forearm, shoulder) receive data from left children
                // Chest has no children, so skip hub client service initialization
                if (deviceConfig.isHubMode() && (newRole == ROLE_RIGHT_HAND || newRole == ROLE_RIGHT_FOREARM || 
                                                 newRole == ROLE_RIGHT_SHOULDER)) {
                    // Initialize hub client service to receive ESP-NOW data from left children
                    setupHubClientService();
                }
                
                // 5. Provide LED feedback
                // TODO: Check LED feedback is working
                startRoleChangeLEDPattern();
                
                // 6. Log final status
                Serial.print("Final status - Role: '");
                Serial.print(deviceConfig.getRoleName(deviceConfig.getRole()));
                Serial.print("', Assigned: ");
                Serial.print(deviceConfig.isRoleAssigned() ? "YES" : "NO");
                Serial.print(", Mode: ");
                Serial.println(deviceConfig.isHubMode() ? "HUB" : "NODE");
                
            } else {
                Serial.println("Failed to apply role change!");
            }
        } else {
            Serial.printf("Invalid role value: %d\n", newRole);
        }
    } else {
        Serial.printf("Unexpected role config data length: %d\n", value.length());
    }
}

void handleCalibration(const std::string& value, bool success) {
    if (!success) {
        Serial.println("HUB: Calibration: Failed to read characteristic value");
        return;
    }
    
    // Only process if this is a HUB device
    if (!deviceConfig.isHubMode()) {
        return;
    }
    
    // Check for calibration command
    if (!value.empty()) {
        uint8_t cmd = static_cast<uint8_t>(value[0]);
        
        if (cmd == 0x01) { // Calibration command
            Serial.println("HUB: Calibration command detected");
            
            // Reset hub's own IMU first
            if (imu.isAvailable()) {
                imu.reset();
                Serial.println("HUB: Hub's own IMU reset");
            }
            
            // Send calibration command to left child via ESP-NOW (right hubs only)
            // Note: Chest has no children, so this will not send anything for chest
            sendCalibrationCommand();
            
            // Reset the GATT characteristic to its original value (empty/0x00)
            // This ensures future calibration commands are properly detected
            if (calibrationChar != nullptr) {
                calibrationChar->setValue((uint8_t*)"", 0);
            }
        }
    }
}

void handleColorChange(const std::string& value, bool success) {
    if (!success) {
        Serial.println("Color Change: Failed to read characteristic value");
        return;
    }
    
    // Expect 3-byte RGB values
    if (value.length() == 3) {
        uint8_t r = value[0];
        uint8_t g = value[1];
        uint8_t b = value[2];
        
        Serial.println("=== COLOR CHANGE DETECTED ===");
        Serial.printf("New color: R=%02X G=%02X B=%02X\n", r, g, b);
        
        // Update color manager (if available)
        // Note: This would need ColorManager to be accessible
        // For now, we'll just log the color change
        
        // Example of how this would work with ColorManager:
        // if (colorManager) {
        //     colorManager.setColor(r, g, b);
        // }
        
        Serial.println("Color change processed");
        
    } else {
        Serial.printf("Color Change: Unexpected value length: %d (expected 3)\n", value.length());
    }
}

void setupPollingSystem() {
    // Initialize the polling manager
    if (!pollingManager.begin()) {
        Serial.println("ERROR: Failed to initialize polling manager!");
        return;
    }
    
    // Enable debug mode for initial setup
    pollingManager.setDebugMode(true);
} 
