Eidon-AI/eidon-tracker/firmware/src/Version.h

#ifndef FIRMWARE_VERSION_H
#define FIRMWARE_VERSION_H

#define FIRMWARE_VERSION_MAJOR 2
#define FIRMWARE_VERSION_MINOR 1
#define FIRMWARE_VERSION_PATCH 0

// String representation for BLE Device Information Service
#define FIRMWARE_VERSION_STRING "2.1.0"

#endif // FIRMWARE_VERSION_H
