Eidon-AI/eidon-tracker/firmware/ext_nimble_config.h

#ifndef EXT_NIMBLE_CONFIG_H
#define EXT_NIMBLE_CONFIG_H

// This file is required by NimBLE but we're using build flags for configuration
// The build flags in platformio.ini will override these settings

#endif // EXT_NIMBLE_CONFIG_H 
