Eidon-AI/eidon-tracker/images/assemble-1-solder-battery.png

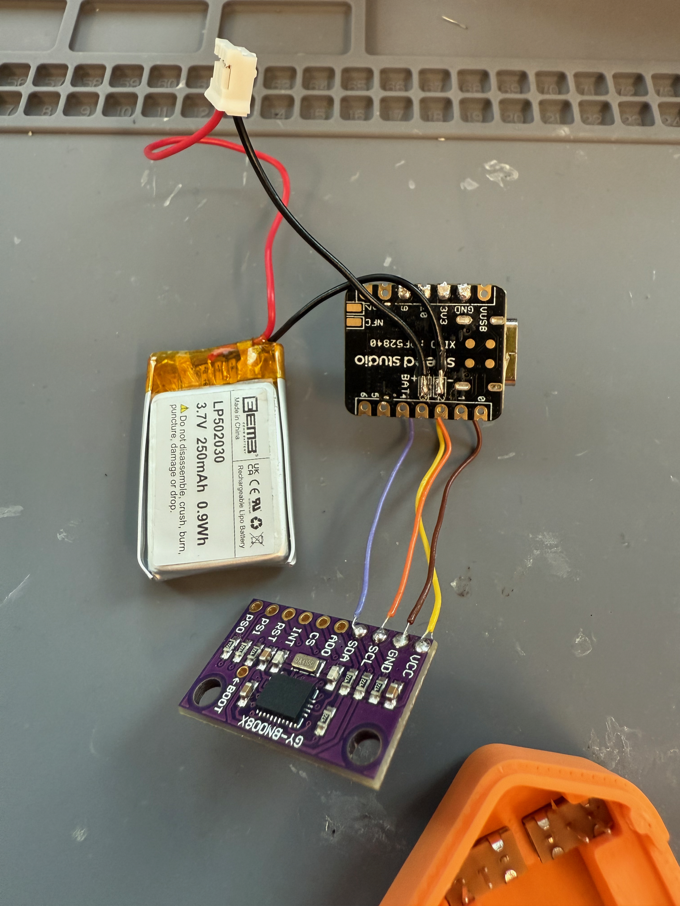
images/assemble-1-solder-battery.png
